krups/amtps-fta-hardware/documentation/images/100g-accel-board.jpg

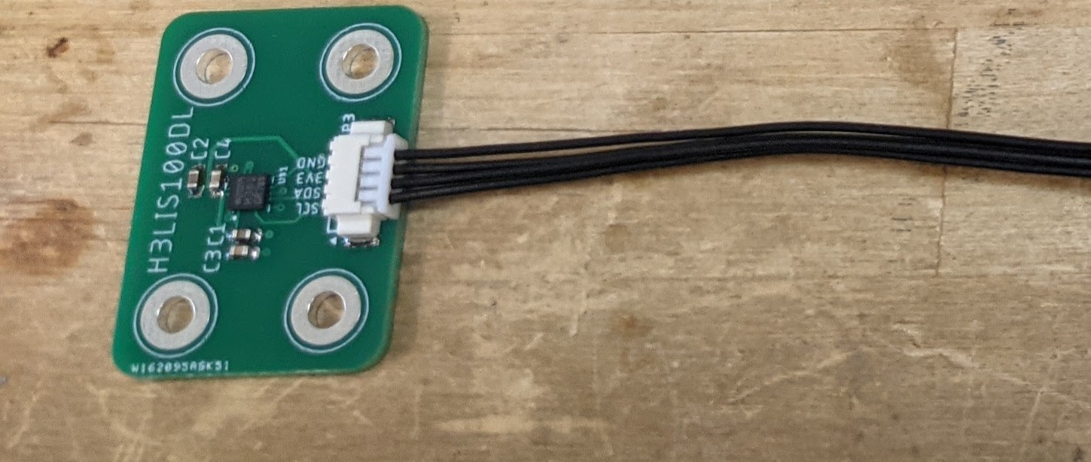
documentation/images/100g-accel-board.jpg
