krups/amtps-fta-hardware/documentation/images/main-board-top.png

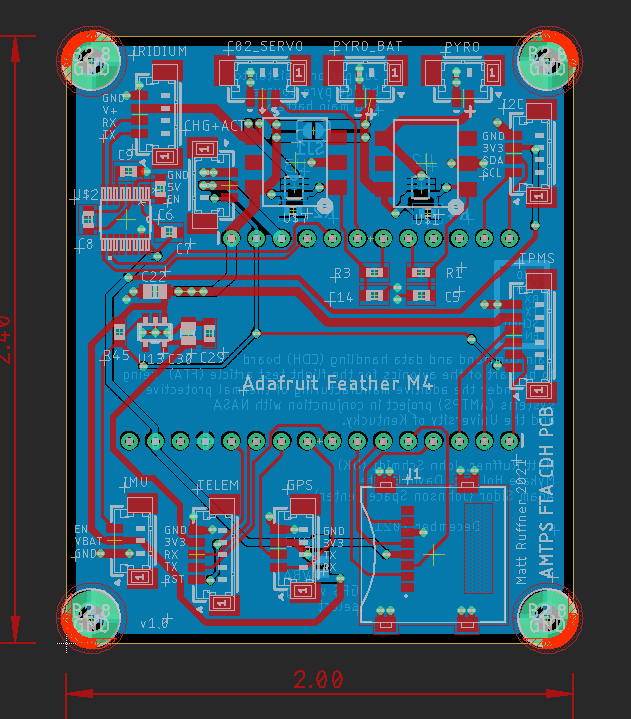
documentation/images/main-board-top.png
