krups/amtps-fta-hardware/documentation/images/ukcoe-pres.png

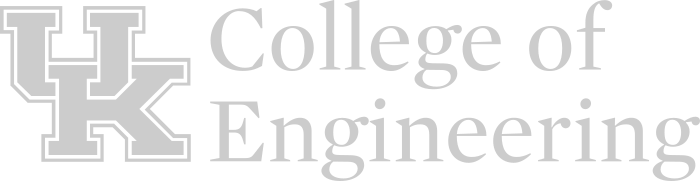
documentation/images/ukcoe-pres.png
