krups/amtps-fta-hardware/documentation/images/ukcoe.png

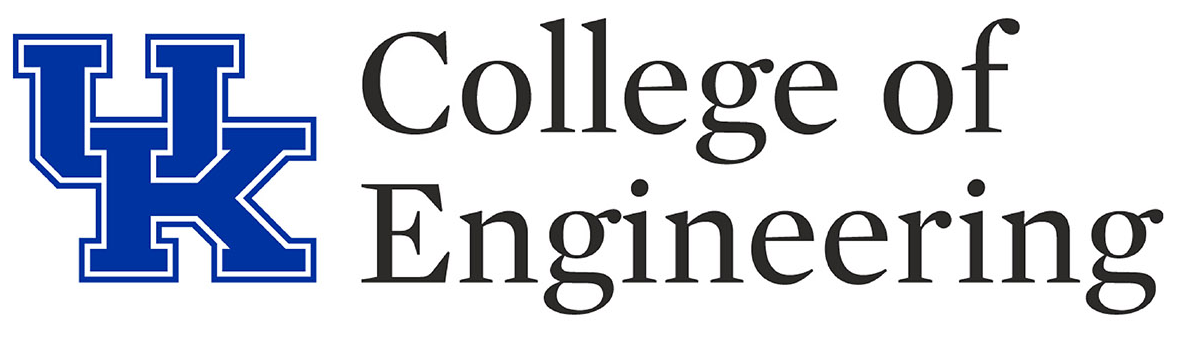
documentation/images/ukcoe.png
