krups/amtps-fta-hardware/pcb/gps_board/images/v0.1-render.png

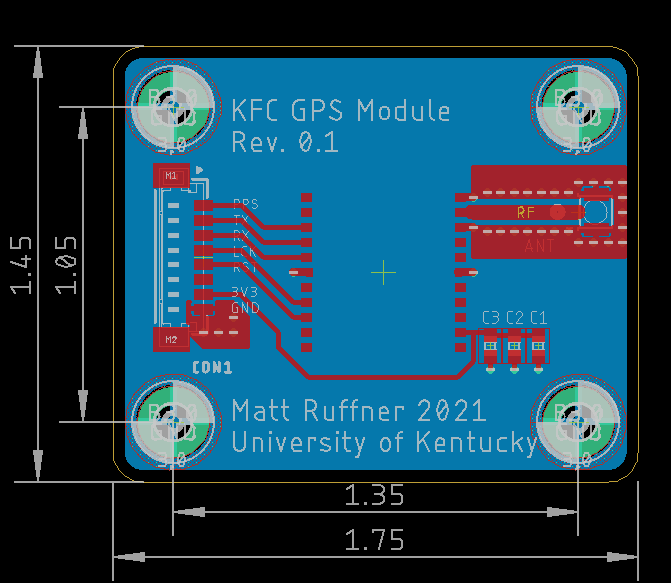
pcb/gps_board/images/v0.1-render.png
