krups/amtps-fta-hardware/pcb/main_board/main_board_bottom.png

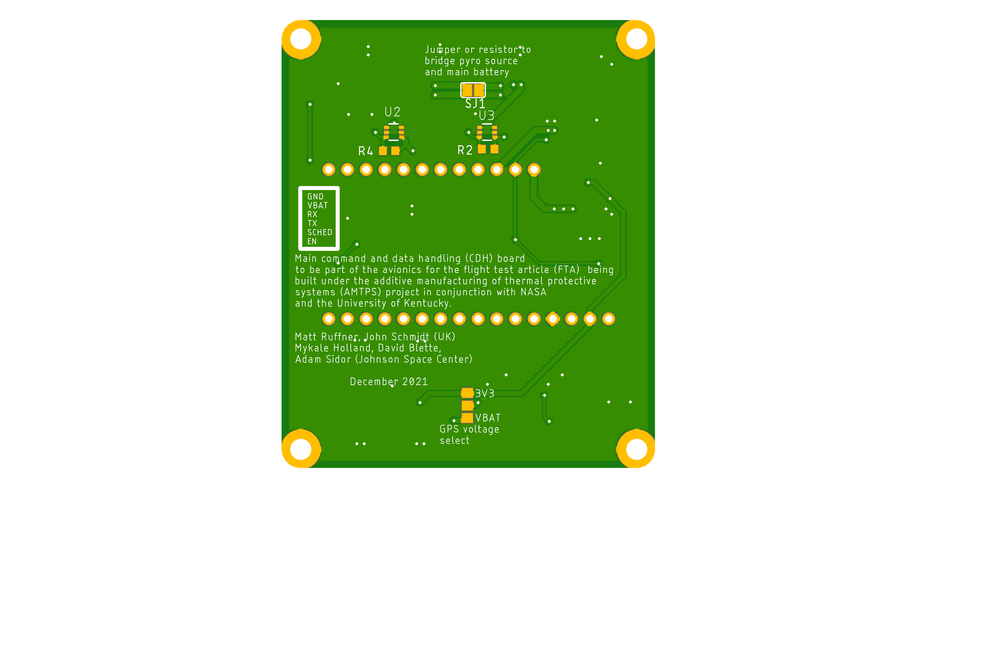
pcb/main_board/main_board_bottom.png
