krups/amtps-fta-hardware/pcb/main_board/main_board_top.png

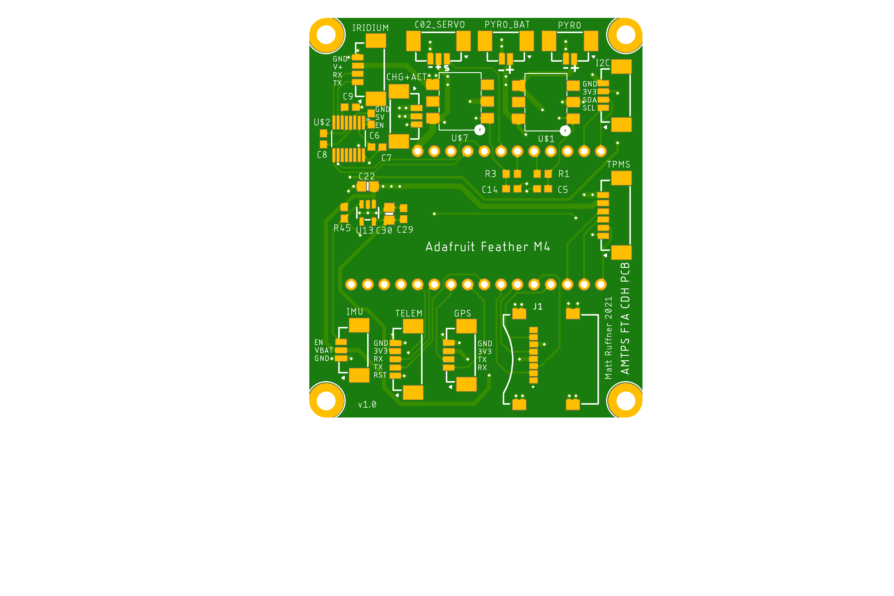
pcb/main_board/main_board_top.png
