krups/amtps-fta-hardware/pcb/tc_board/tc_board_bottom.png

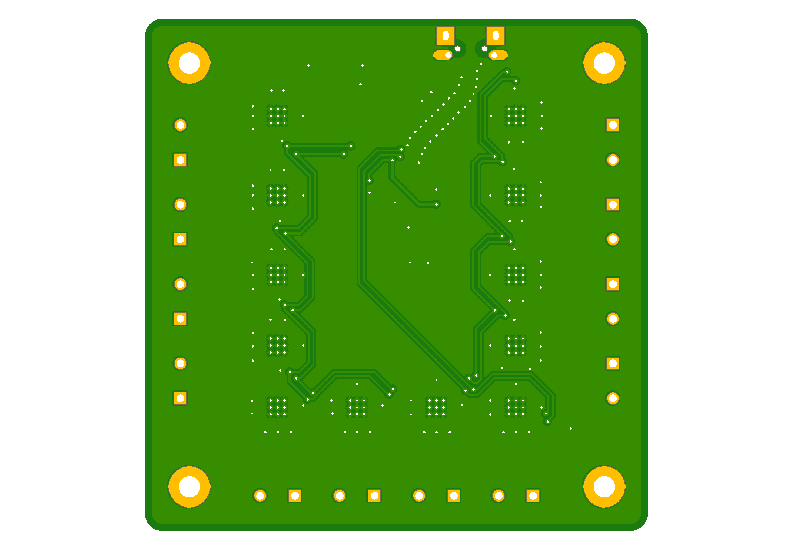
pcb/tc_board/tc_board_bottom.png
