krups/amtps-fta-hardware/pcb/tc_board/tc_board_top.png

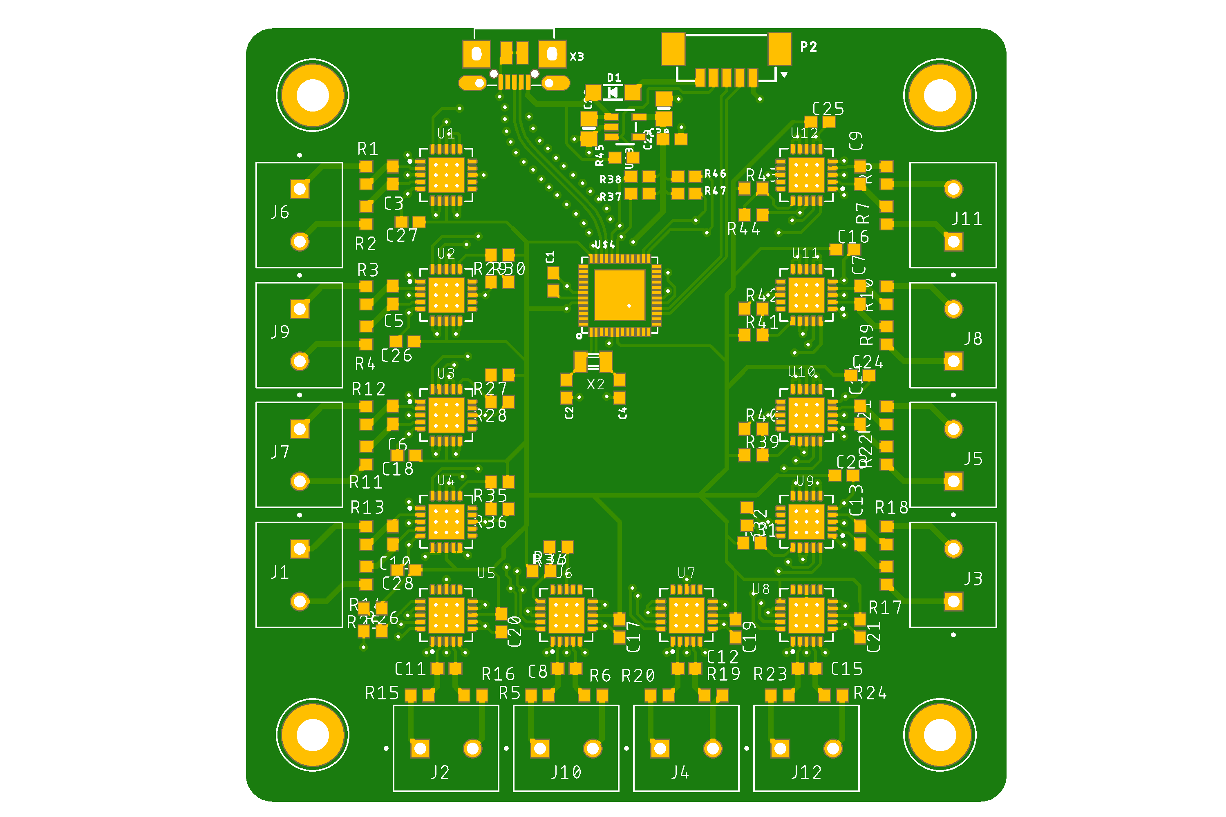
pcb/tc_board/tc_board_top.png
