krups/amtps-fta-hardware/pcb/tc_breakout/images/tc_breakout_bottom.png

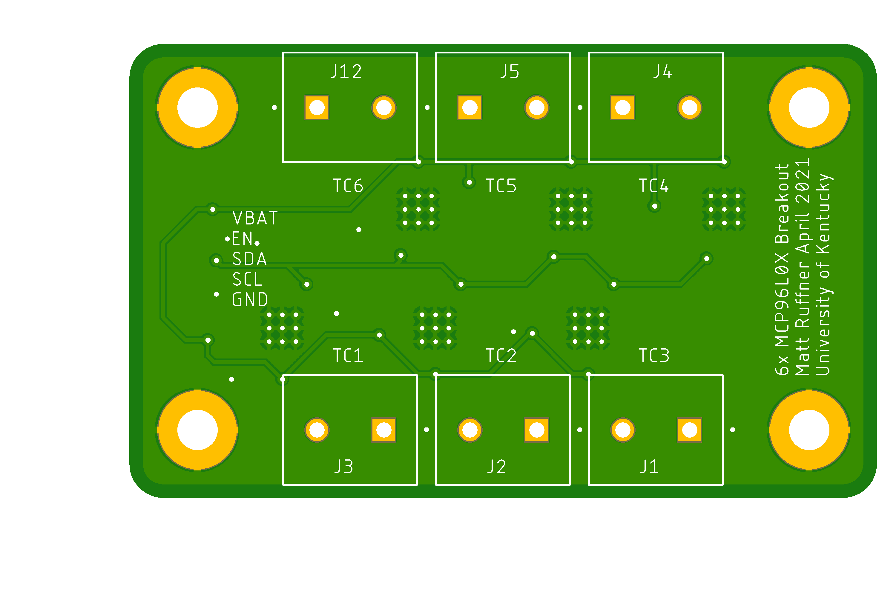
pcb/tc_breakout/images/tc_breakout_bottom.png
