krups/amtps-fta-hardware/pcb/tc_breakout/images/tc_breakout_render.png

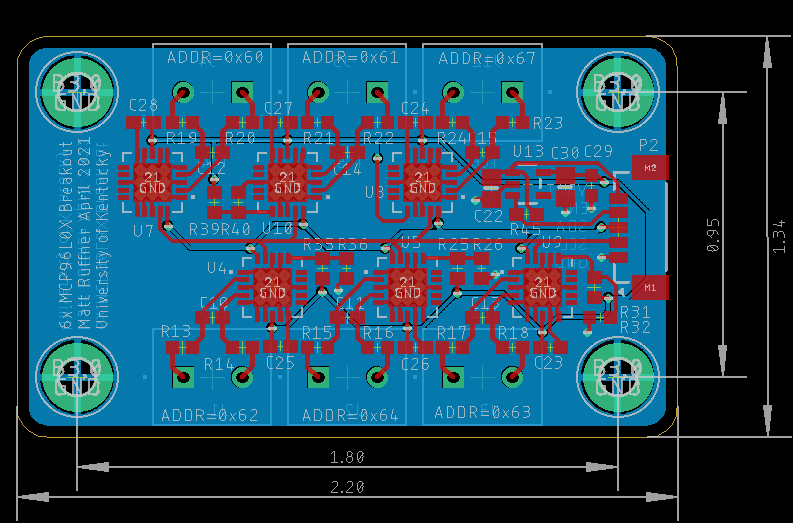
pcb/tc_breakout/images/tc_breakout_render.png
