krups/amtps-fta-hardware/pictures/v1boards-white.png

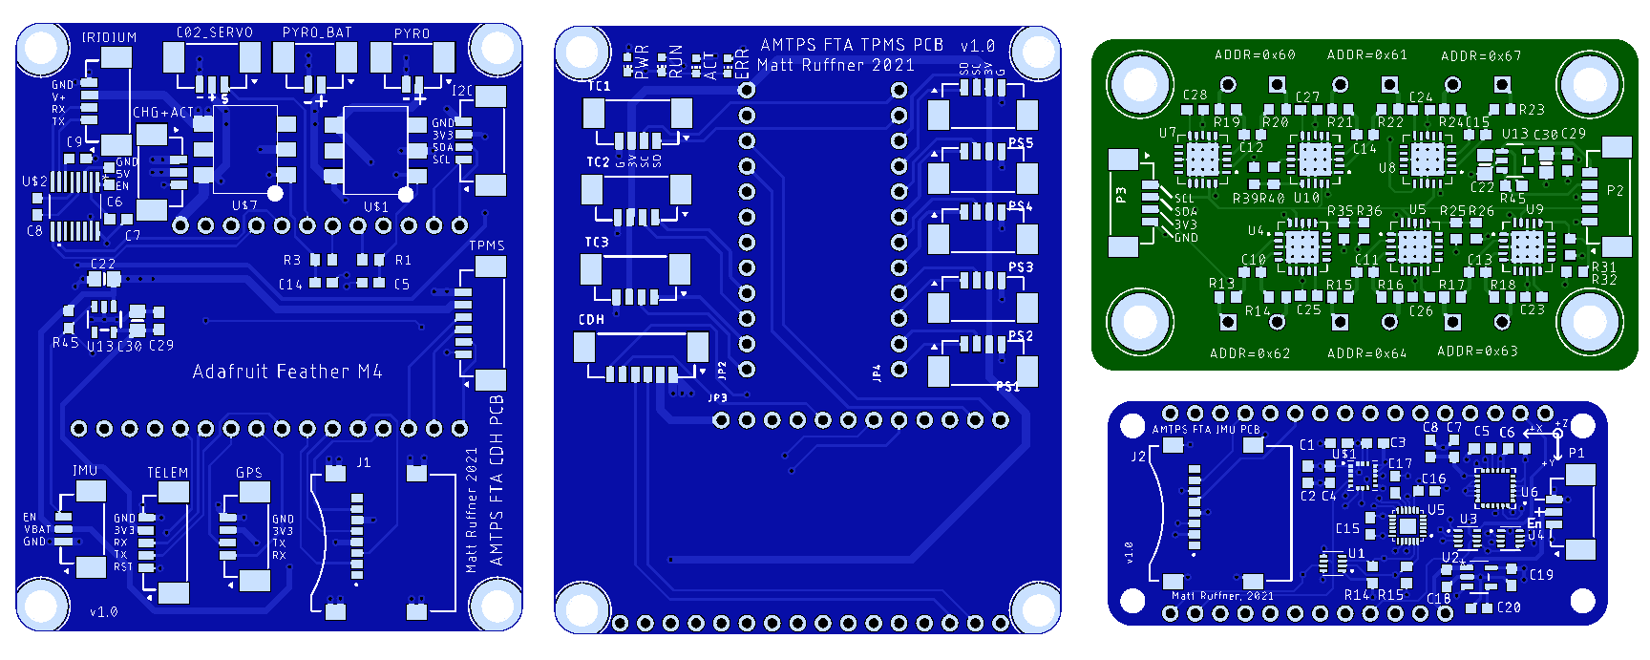
pictures/v1boards-white.png
