krups/amtps-fta-hardware/pictures/v1boards.png

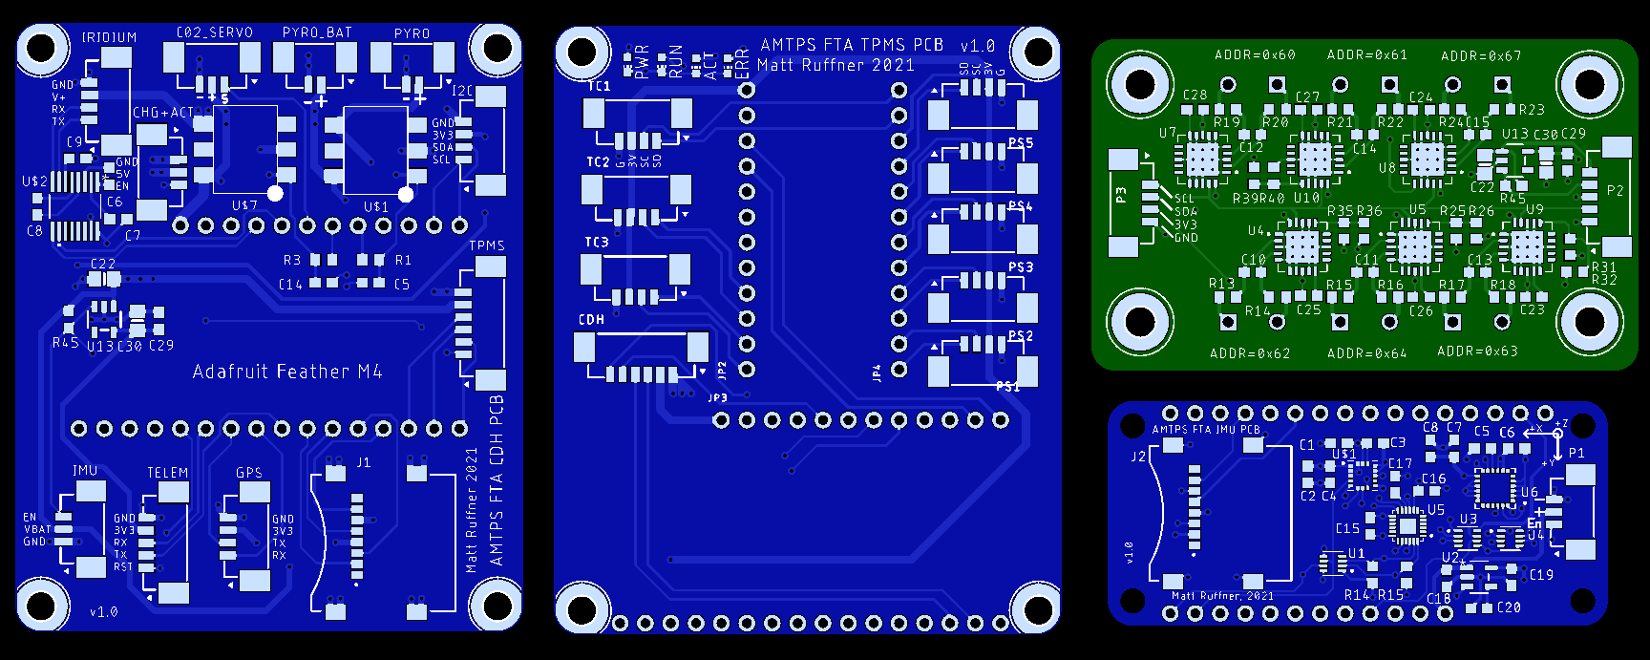
pictures/v1boards.png
