krups/amtps-fta-hardware/pictures/v1imulogger.png

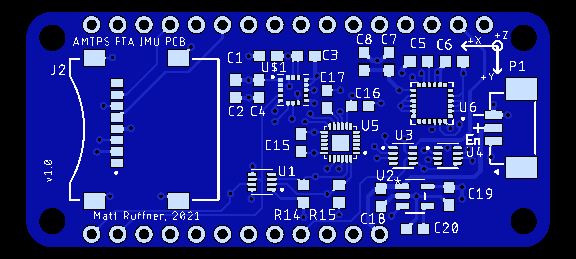
pictures/v1imulogger.png
