krups/amtps-fta-hardware/pictures/v1mainboard.png

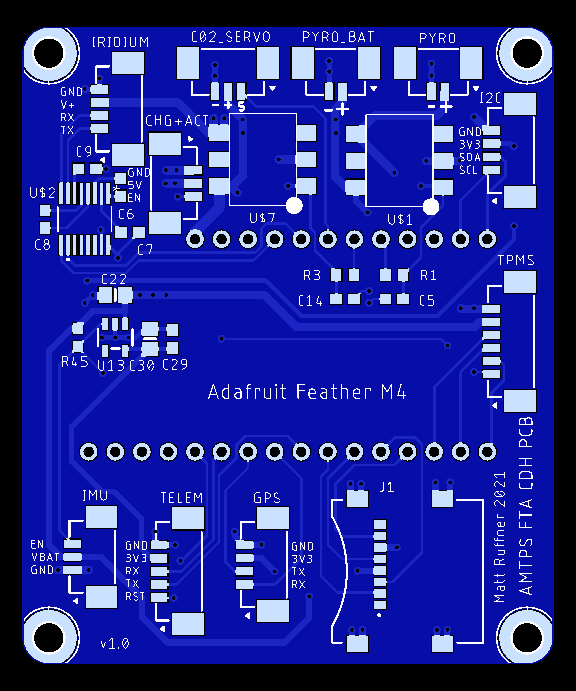
pictures/v1mainboard.png
