krups/amtps-fta-hardware/pictures/v1tcbreakout.png

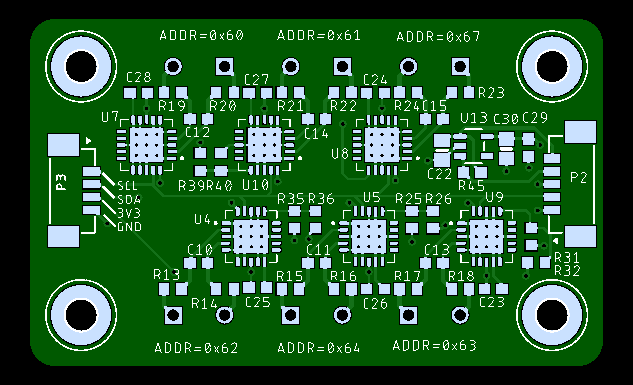
pictures/v1tcbreakout.png
