krups/amtps-fta-hardware/pictures/v1tpms.png

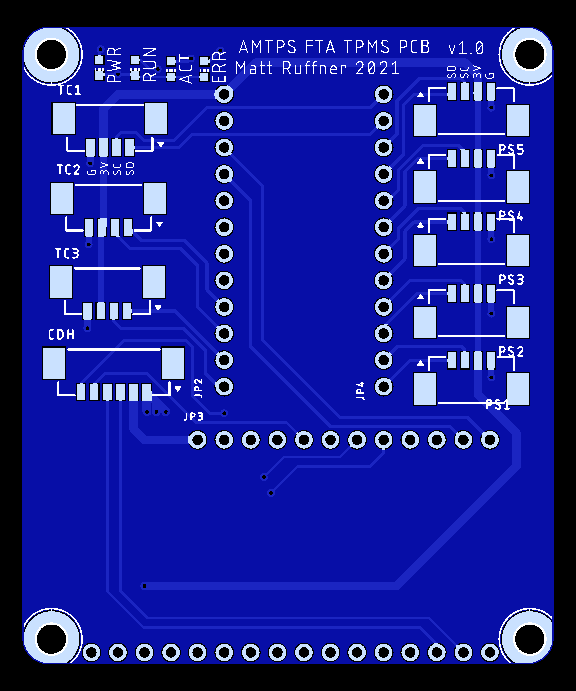
pictures/v1tpms.png
